jeffqchen/BVM-Faceplate/D14H5/4by3/Individual/[Grey][4x]Arrow.stl

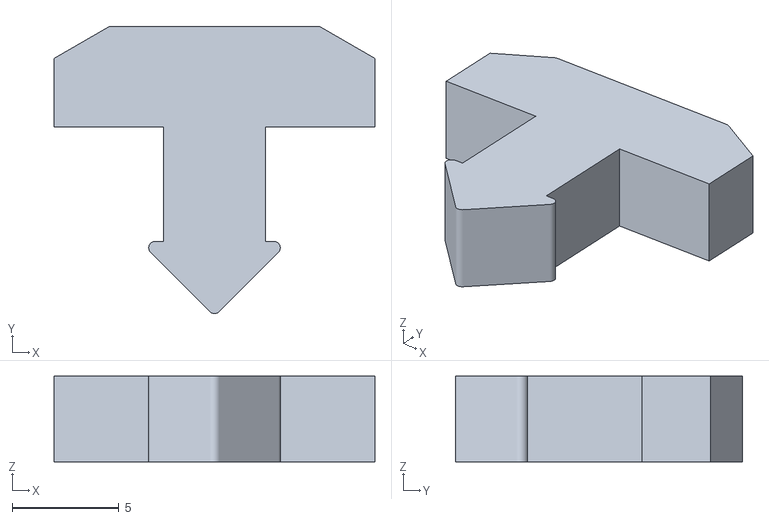
[picture p42: CAD file, 2021-11-20]
D14H5/4by3/Individual/[Grey][4x]Arrow.stl
15.0 x 13.4 x 4.00
