jeffqchen/BVM-Faceplate/D14H5/4by3/Individual/[Grey]BR.stl

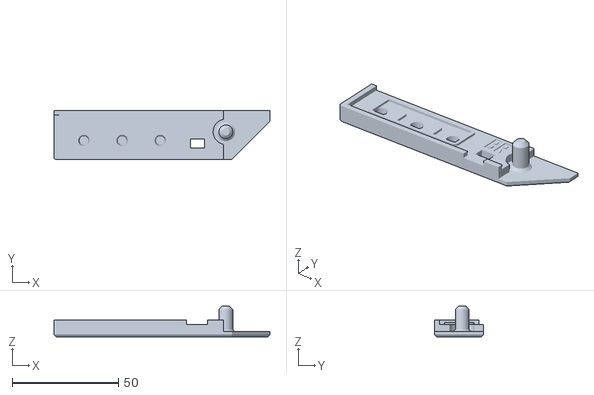
[picture p43: CAD file, 2021-11-20]
D14H5/4by3/Individual/[Grey]BR.stl
101.8 x 23.0 x 14.4
