jeffqchen/BVM-Faceplate/D14H5/4by3/Individual/[Black]Inner DR.stl

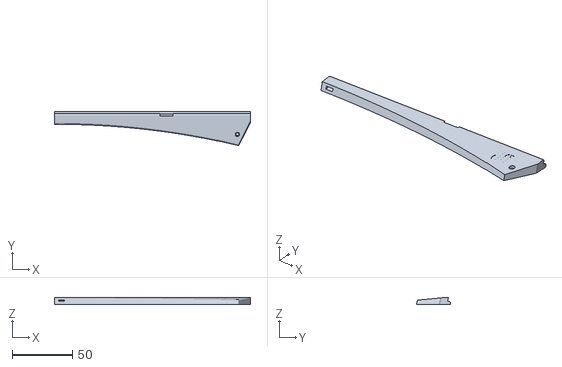
[picture p44: CAD file, 2021-11-20]
D14H5/4by3/Individual/[Black]Inner DR.stl
162.1 x 28.4 x 6.14
