jeffqchen/BVM-Faceplate/D14H5/4by3/Individual/[Black]Inner L.stl

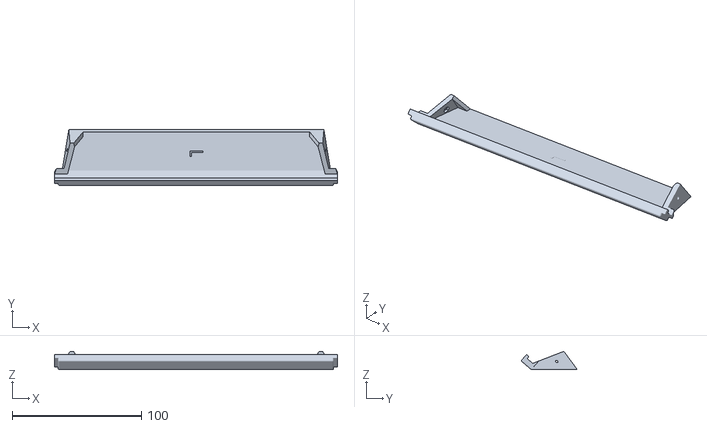
[picture p45: CAD file, 2021-11-20]
D14H5/4by3/Individual/[Black]Inner L.stl
218.6 x 43.1 x 14.2
