jeffqchen/BVM-Faceplate/D14H5/4by3/Individual/[Grey]BM.stl

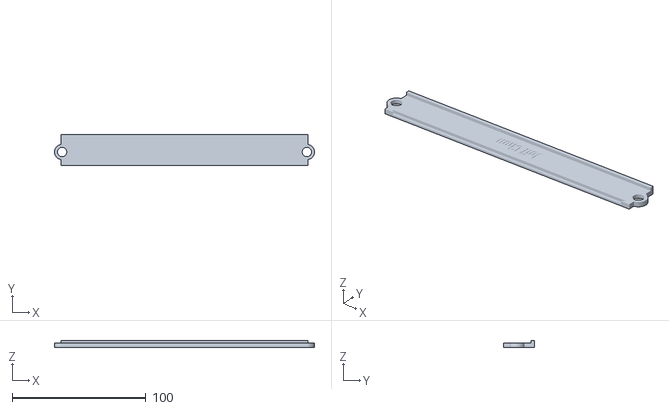
[picture p46: CAD file, 2021-11-20]
D14H5/4by3/Individual/[Grey]BM.stl
194.6 x 23.0 x 5.30
